mirage335/ElectronicsWorkstation/Tabletop/Materials/2x4_tabletop.SLDPRT

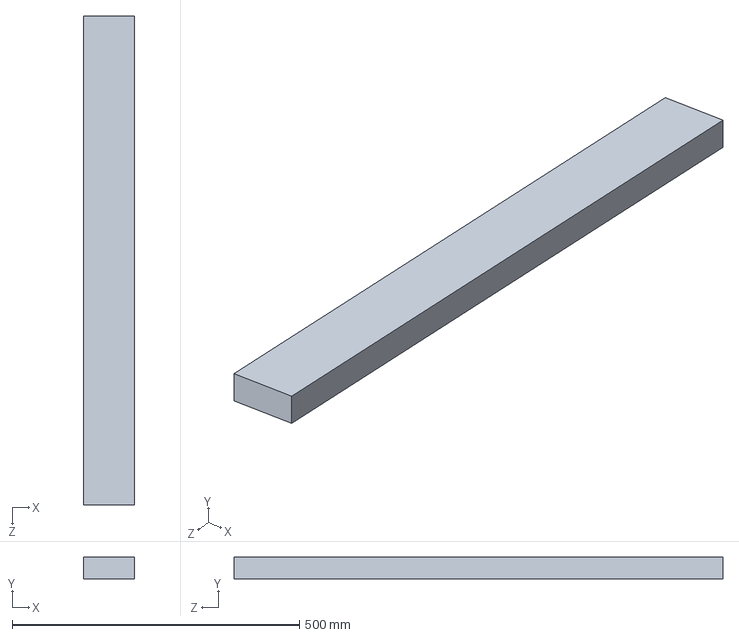
[picture p16: CAD file, 2015-05-22]
Tabletop/Materials/2x4_tabletop.SLDPRT
88.9 x 38.1 x 850.9 mm
