mirage335/ElectronicsWorkstation/Ref/Materials/2x4_desk.SLDPRT

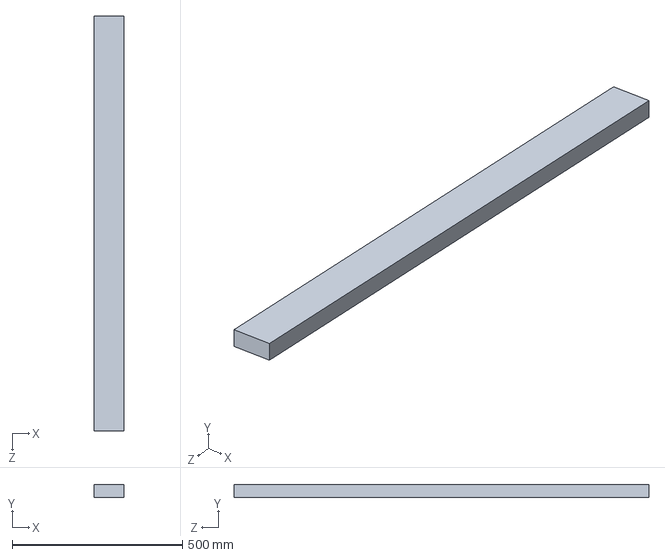
[picture p17: CAD file, 2015-05-22]
Ref/Materials/2x4_desk.SLDPRT
88.9 x 38.1 x 1219.2 mm
